oldgerman/ESP32-C3-DEV-M-1/Datasheets/cp2102给低功耗设备复位.png

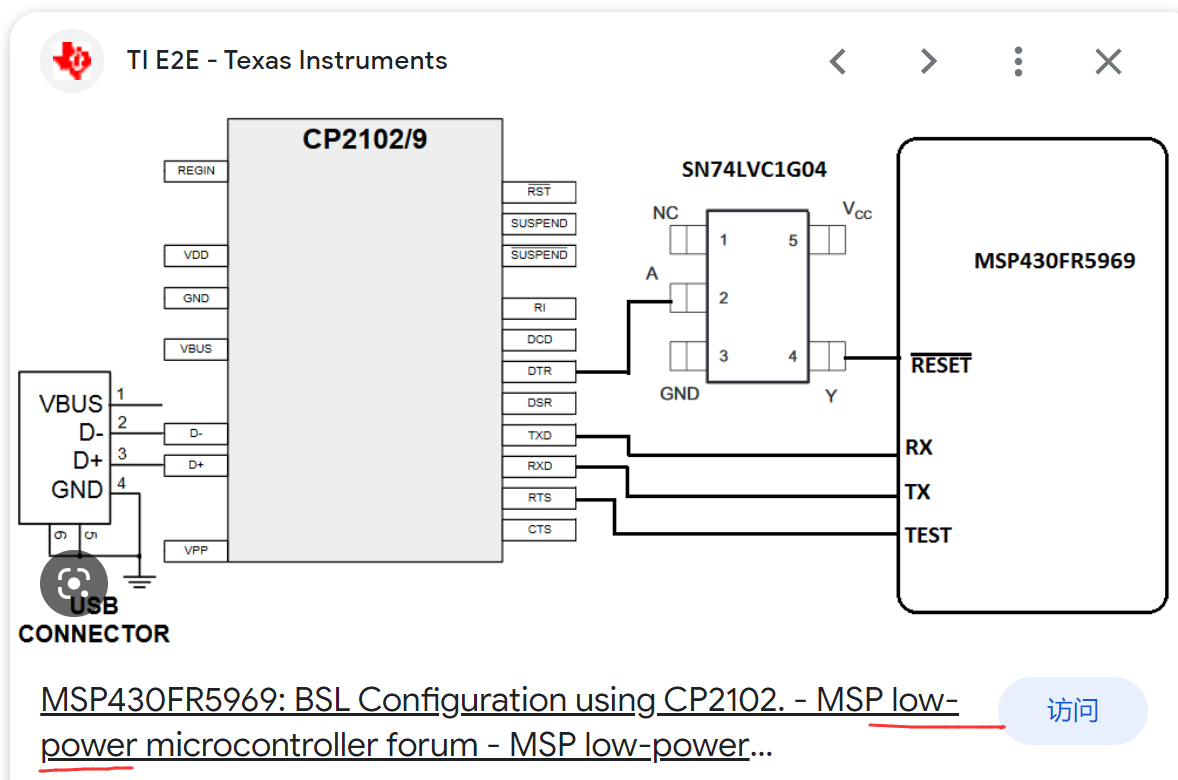
Datasheets/cp2102给低功耗设备复位.png
