oldgerman/ESP32-C3-DEV-M-1/Datasheets/ESP32-C3FH4AZ芯片的封装未引出GPIO12~17，在封装内接4MB FLASH.png

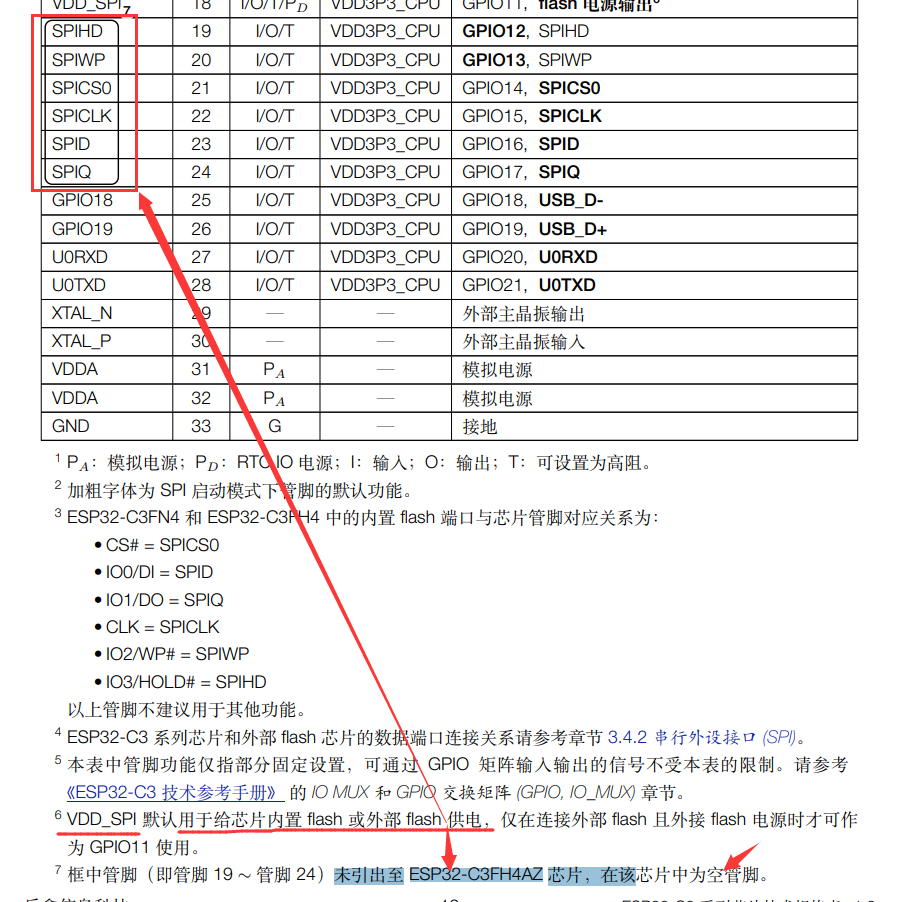
Datasheets/ESP32-C3FH4AZ芯片的封装未引出GPIO12~17，在封装内接4MB FLASH.png
