oldgerman/ESP32-C3-DEV-M-1/Datasheets/Figure 4.3. Transmit and Receive Toggle.png

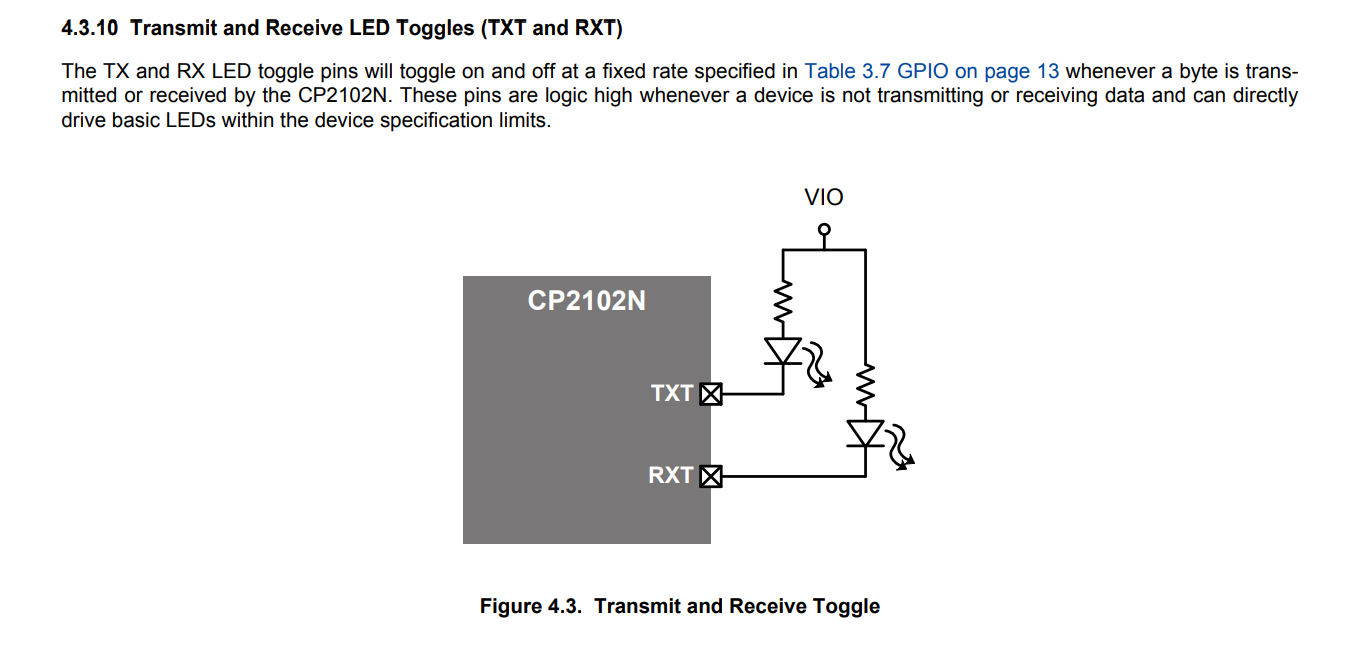
Datasheets/Figure 4.3. Transmit and Receive Toggle.png
