oldgerman/ESP32-C3-DEV-M-1/Images/初号机(2).JPG

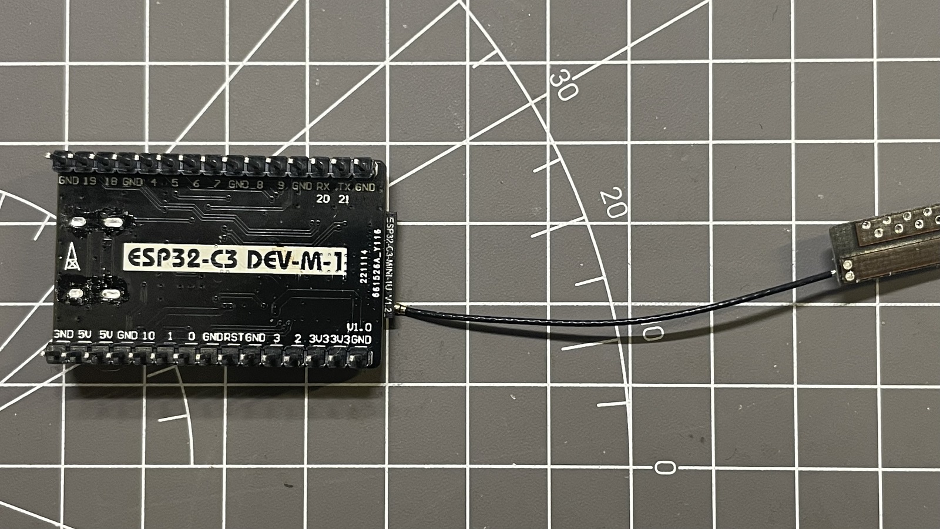
Images/初号机(2).JPG
