oldgerman/ESP32-C3-DEV-M-1/Reference/ESP32-C3-DEVKITM-1/ESP32-C3-DEVKITM-1 PCB Layout/ESP32-C3-DEVKITM-1(1).png

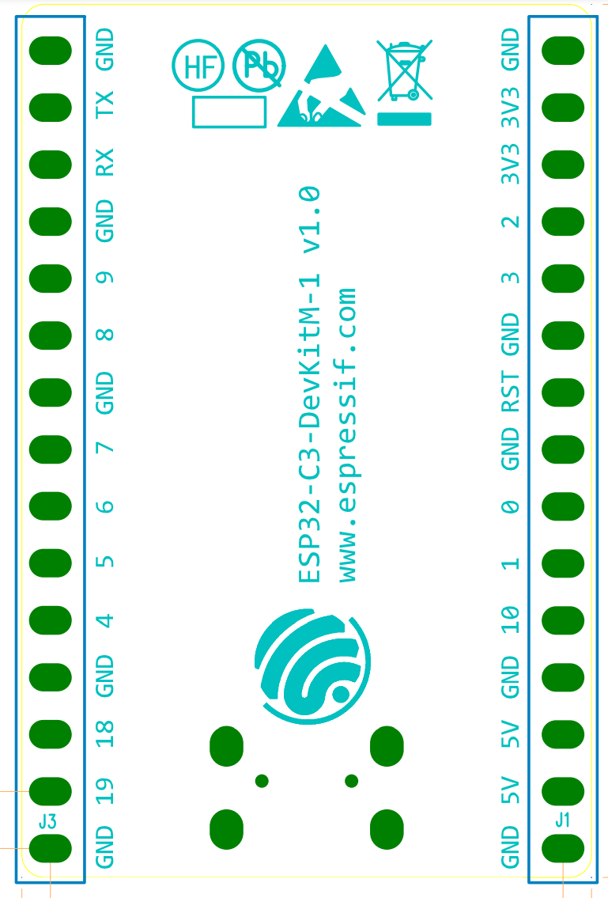
Reference/ESP32-C3-DEVKITM-1/ESP32-C3-DEVKITM-1 PCB Layout/ESP32-C3-DEVKITM-1(1).png
