oldgerman/ESP32-C3-DEV-M-1/Reference/ESP32-C3-DEVKITM-1/Images/ESP32-C3-DEVKITM-1_Brd(3).JPG

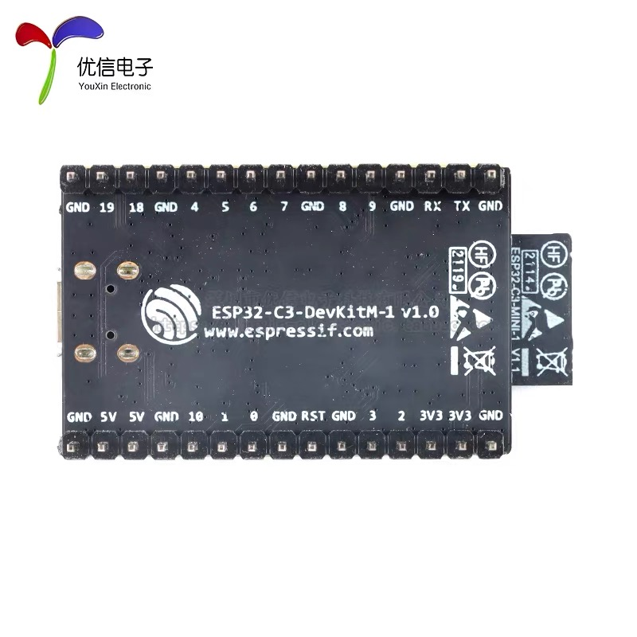
Reference/ESP32-C3-DEVKITM-1/Images/ESP32-C3-DEVKITM-1_Brd(3).JPG
