oldgerman/ESP32-C3-DEV-M-1/Reference/esp32-c3-mini-1/ESP32-C3-MINI-1U-H4_常温版.png

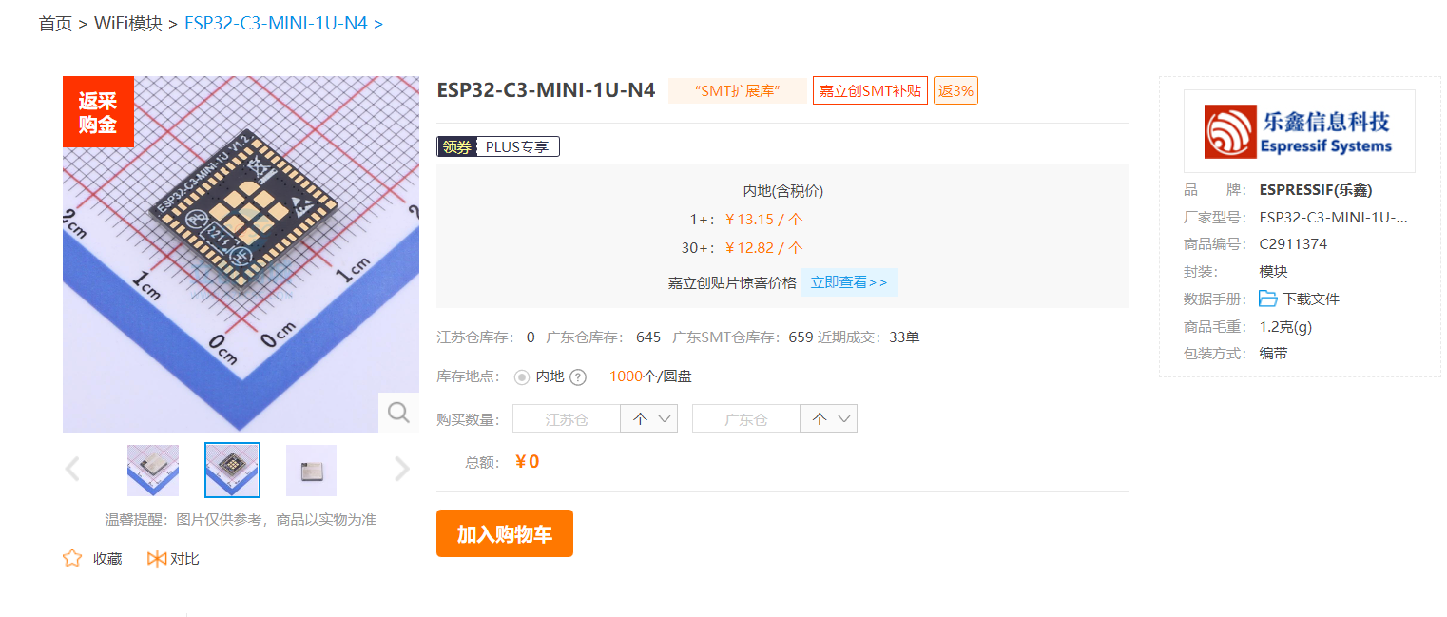
Reference/esp32-c3-mini-1/ESP32-C3-MINI-1U-H4_常温版.png
