oldgerman/ESP32-C3-DEV-M-1/Reference/esp32-c3-mini-1/esp32_c3_mini.jpg

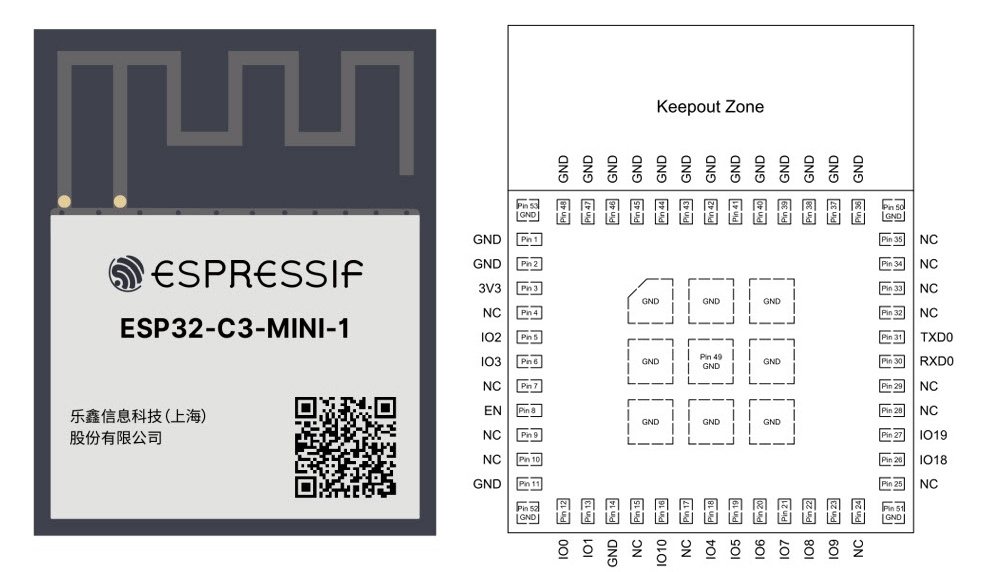
Reference/esp32-c3-mini-1/esp32_c3_mini.jpg
