oldgerman/ESP32-C3-DEV-M-1/Reference/esp32-c3-mini-1/ESP32­C3­MINI-xxx模组机械尺寸.png

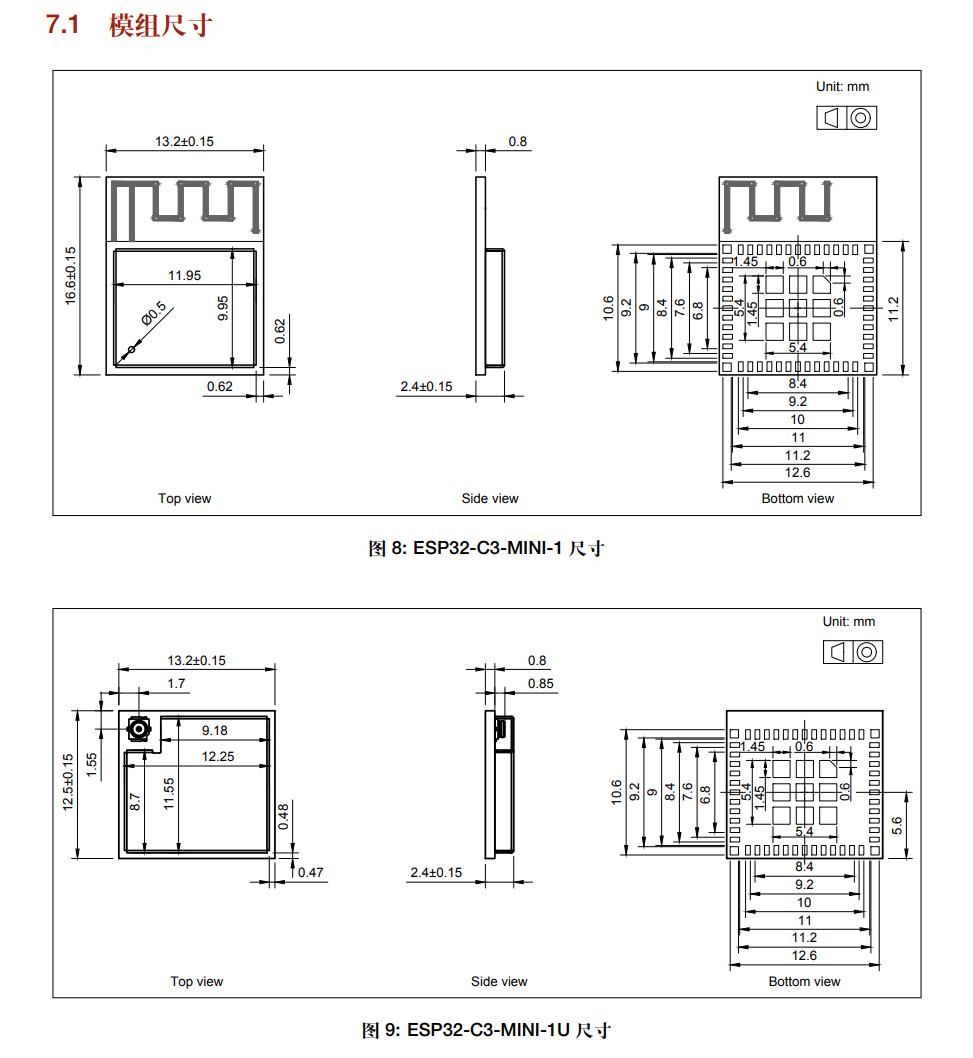
Reference/esp32-c3-mini-1/ESP32­C3­MINI-xxx模组机械尺寸.png
