oldgerman/ESP32-C3-DEV-M-1/Reference/esp32-c3-mini-1/esp-c3-mini-1_PCB_Back.jpg

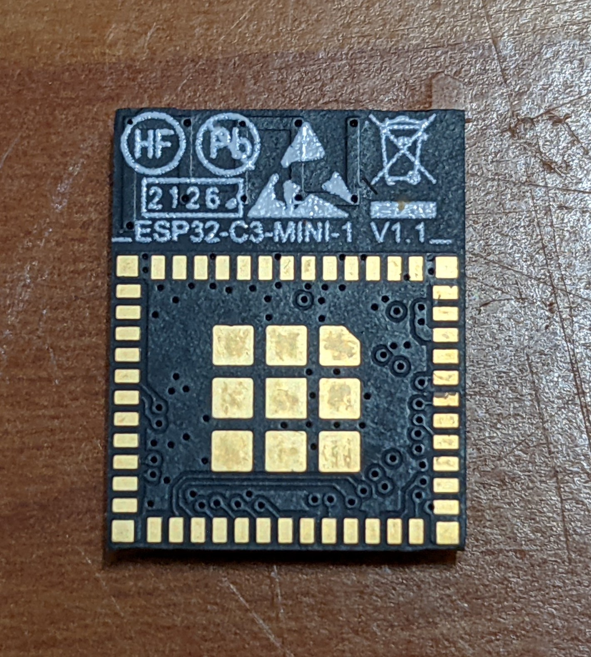
Reference/esp32-c3-mini-1/esp-c3-mini-1_PCB_Back.jpg
