oldgerman/ESP32-C3-DEV-M-1/Reference/esp32-c3-mini-1/esp-c3-mini-1u_PCB_Back.JPG

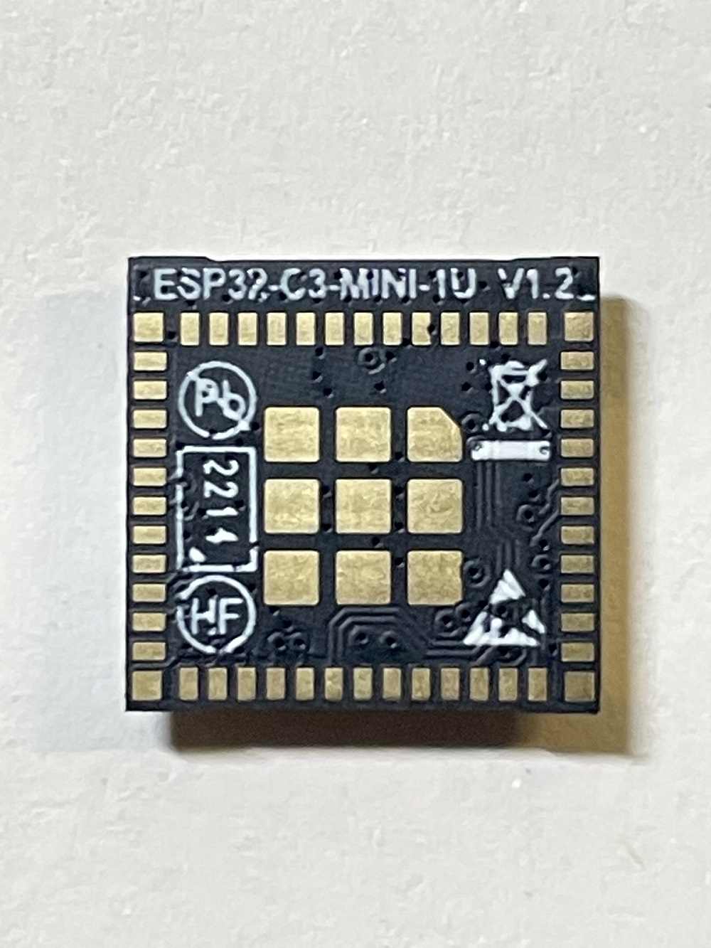
Reference/esp32-c3-mini-1/esp-c3-mini-1u_PCB_Back.JPG
