oldgerman/ESP32-C3-DEV-M-1/Reference/esp32-c3-mini-1/Figure 14 Keepout Zone for ESP32­C3 Module’s Antenna on the Base Board.png

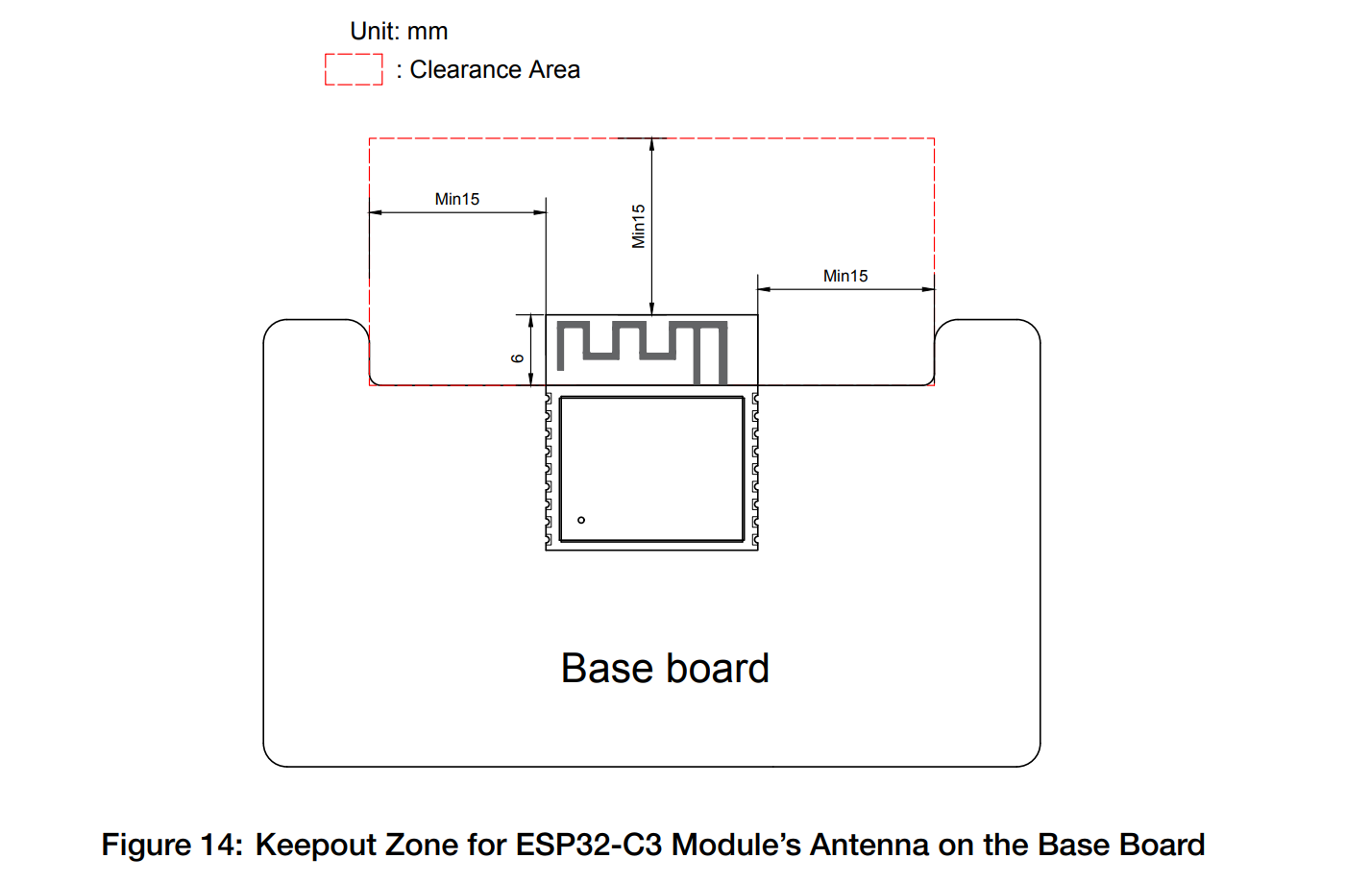
Reference/esp32-c3-mini-1/Figure 14 Keepout Zone for ESP32­C3 Module’s Antenna on the Base Board.png
