oldgerman/ESP32-C3-DEV-M-1/Reference/esp32-c3-mini-1/IPEX-连接器/esp32-c3-mini模组使用IPEX-3代连接器.png

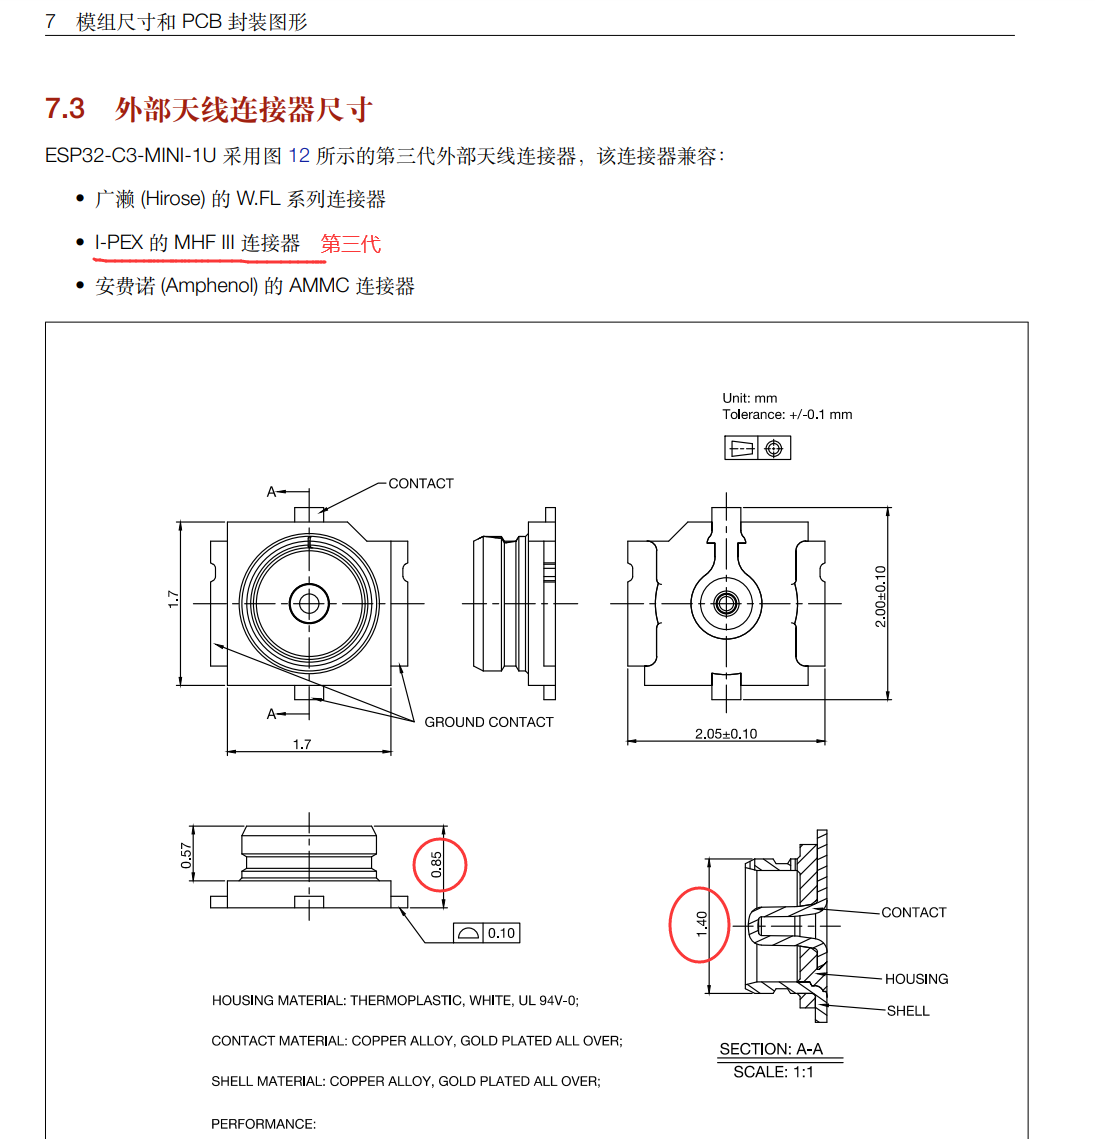
Reference/esp32-c3-mini-1/IPEX-连接器/esp32-c3-mini模组使用IPEX-3代连接器.png
