oldgerman/ESP32-C3-DEV-M-1/Reference/esp32-c3-mini-1/IPEX-连接器/ipex 1、4、3代对比，其中第三代最小，是esp32-c3-mini模组使用的.png

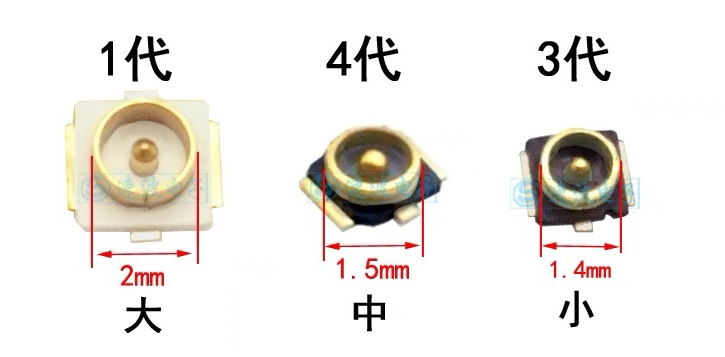
Reference/esp32-c3-mini-1/IPEX-连接器/ipex 1、4、3代对比，其中第三代最小，是esp32-c3-mini模组使用的.png
