oldgerman/ESP32-C3-DEV-M-1/Reference/esp32-c3-mini-1/SnapEDA ESP32-C3-MINI-1-N4 footprint & symbol by Espressif Systems.png

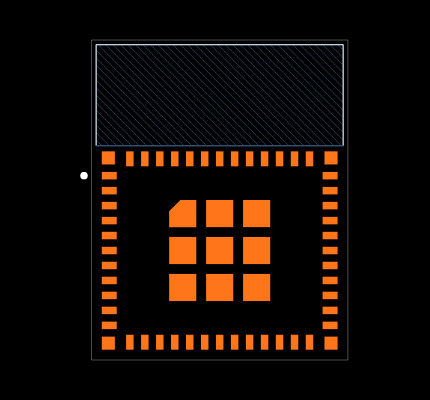
Reference/esp32-c3-mini-1/SnapEDA ESP32-C3-MINI-1-N4 footprint & symbol by Espressif Systems.png
