oldgerman/ESP32-C3-DEV-M-1/Reference/esp32-c3-mini-1/图 9： ESP32­C3­MINI­1U 尺寸.png

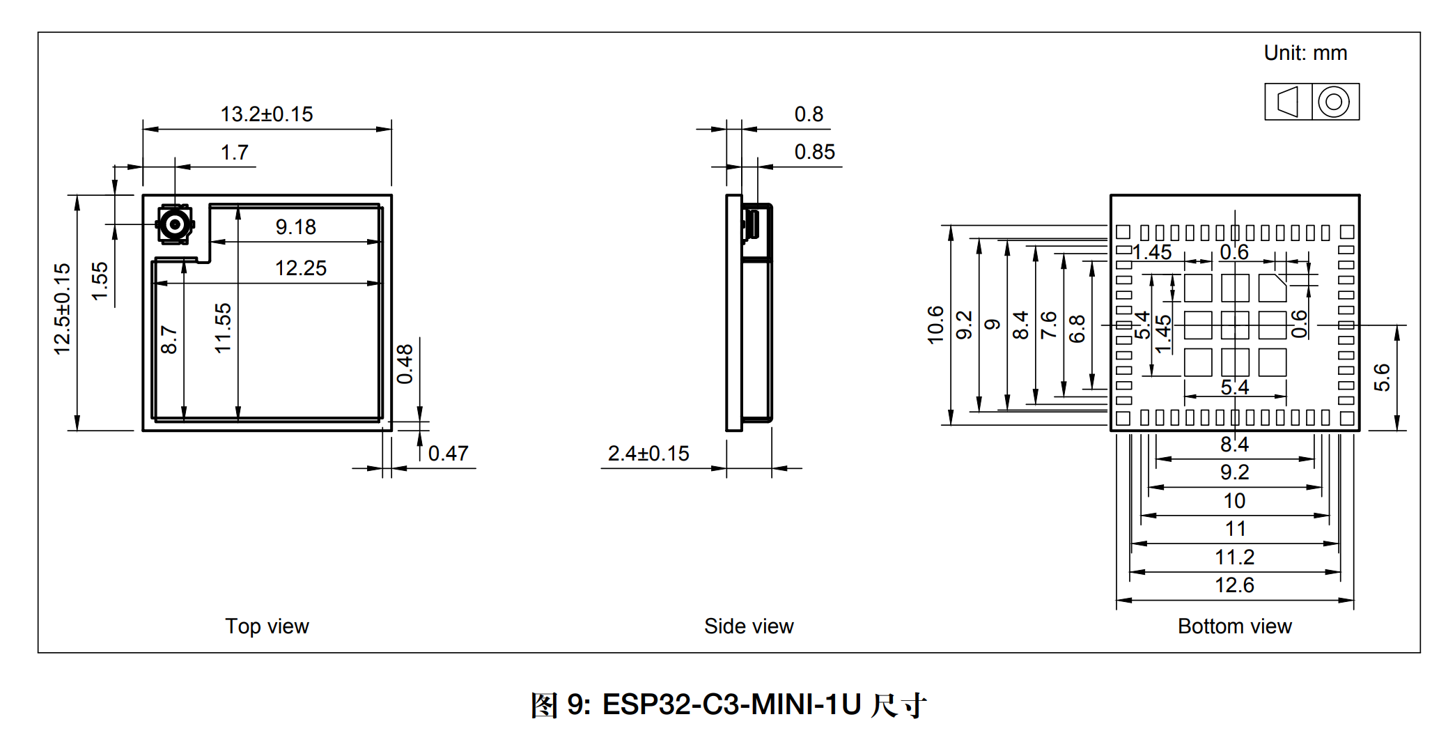
Reference/esp32-c3-mini-1/图 9： ESP32­C3­MINI­1U 尺寸.png
