oldgerman/ESP32-C3-DEV-M-1/Reference/esp32-c3/esp32-c3 U0TXD串499R电阻抑制80MHz谐波.png

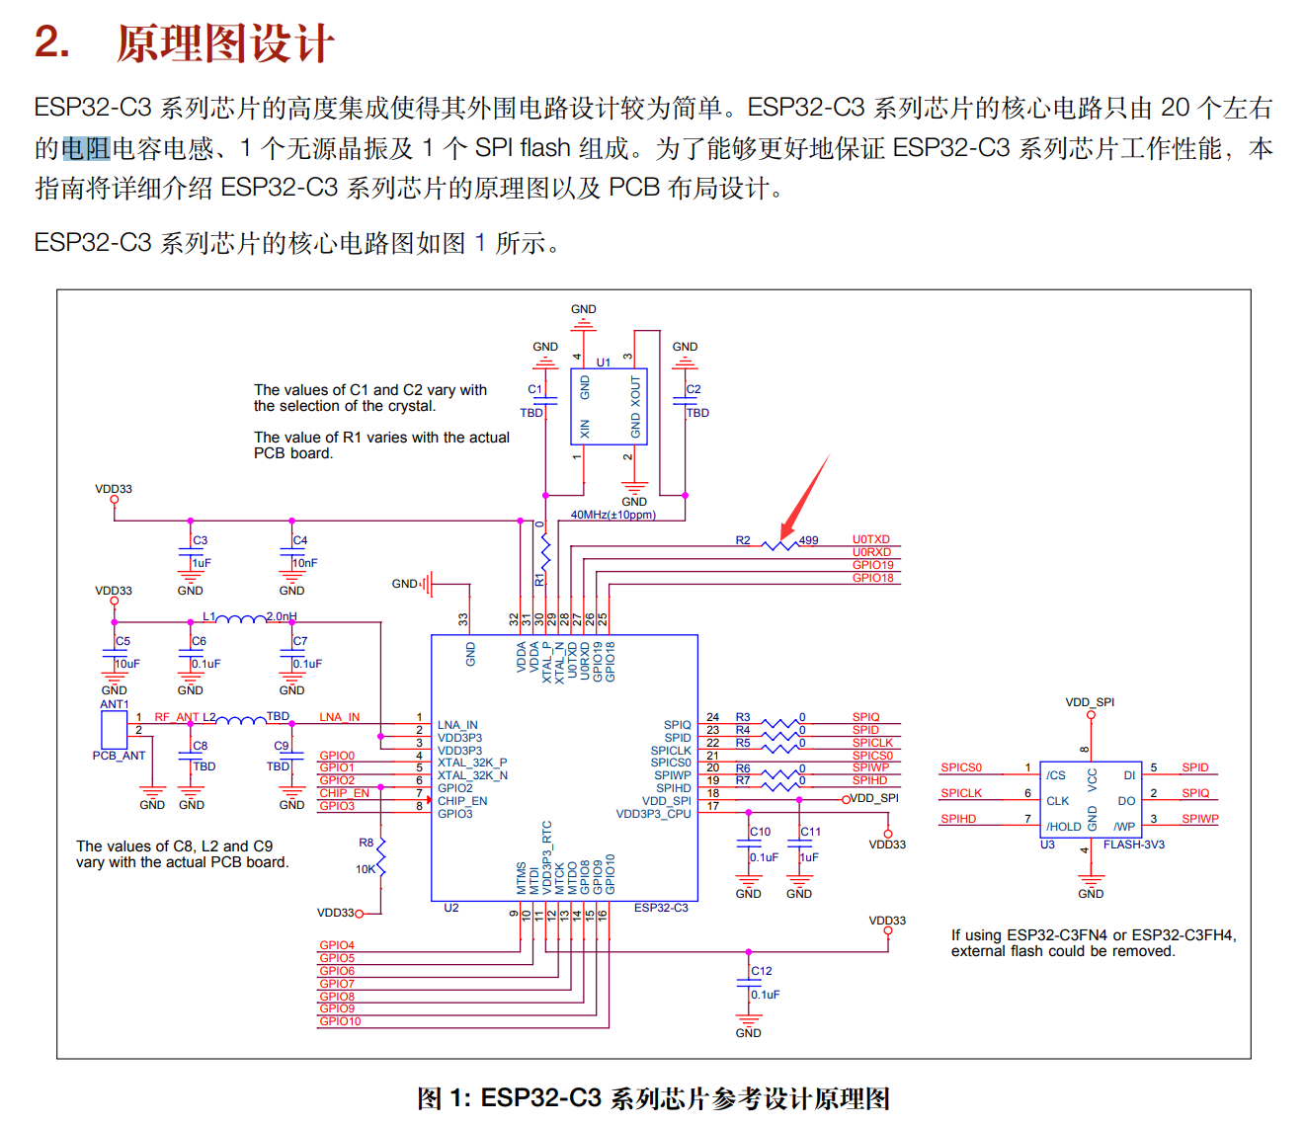
Reference/esp32-c3/esp32-c3 U0TXD串499R电阻抑制80MHz谐波.png
