oldgerman/ESP32-C3-DEV-M-1/Reference/esp32-c3/esp32-c3的USB串口引脚集成内部上拉电阻.png

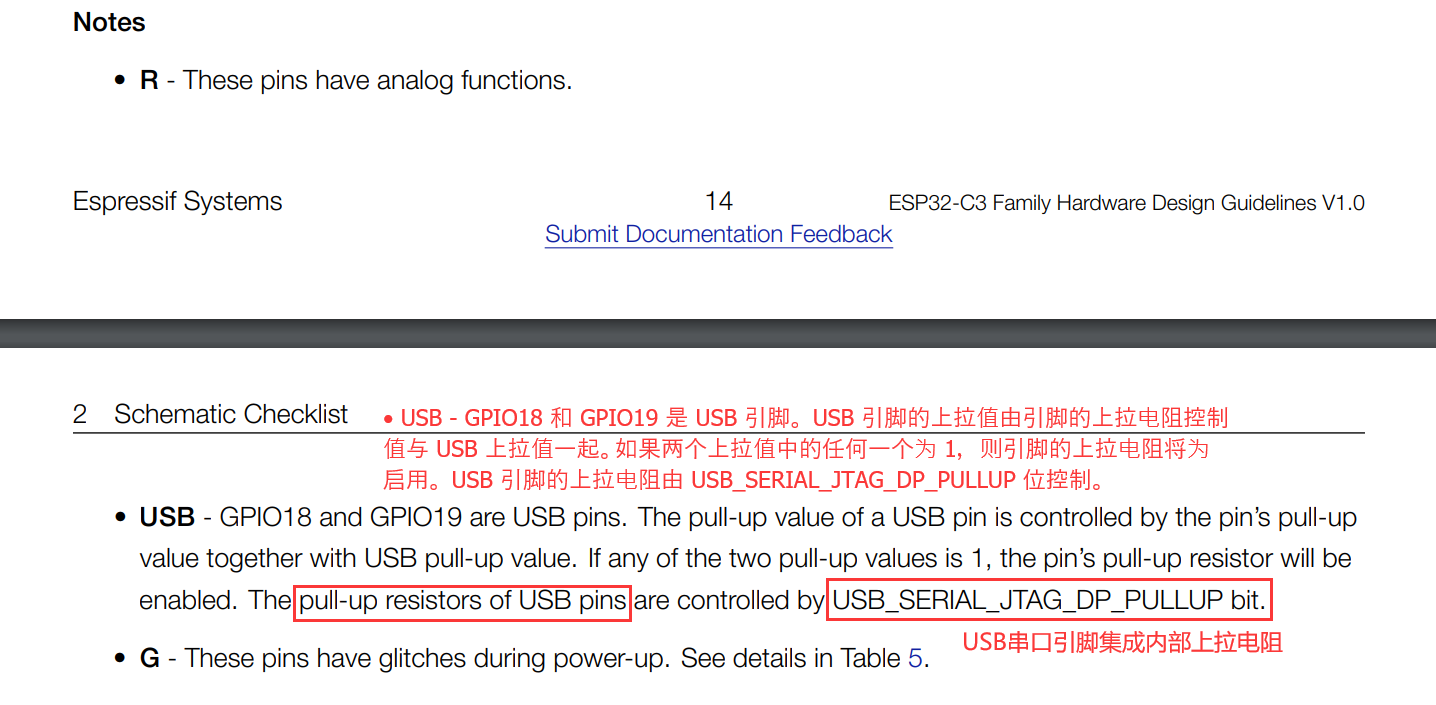
Reference/esp32-c3/esp32-c3的USB串口引脚集成内部上拉电阻.png
